qteck/Laboratory-MMC-controller/Images/acquisition_front.jpg

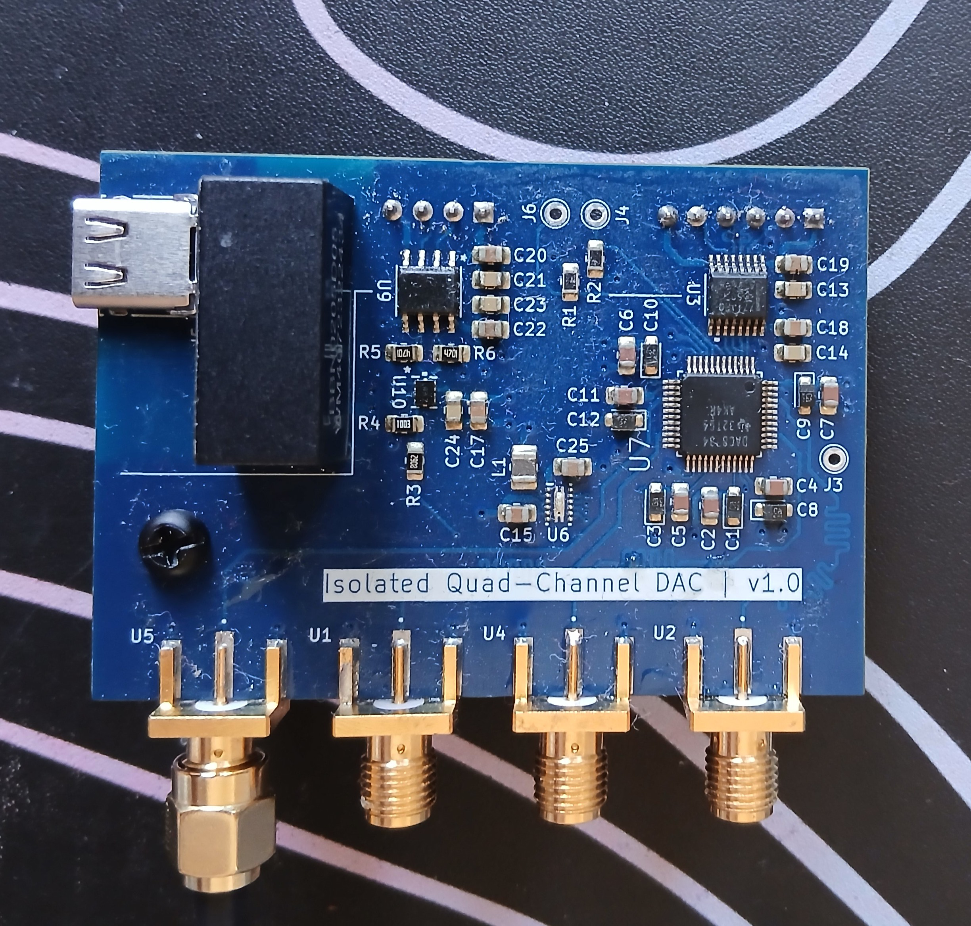
Images/acquisition_front.jpg
