qteck/Laboratory-MMC-controller/Images/df_robot_back.jpg

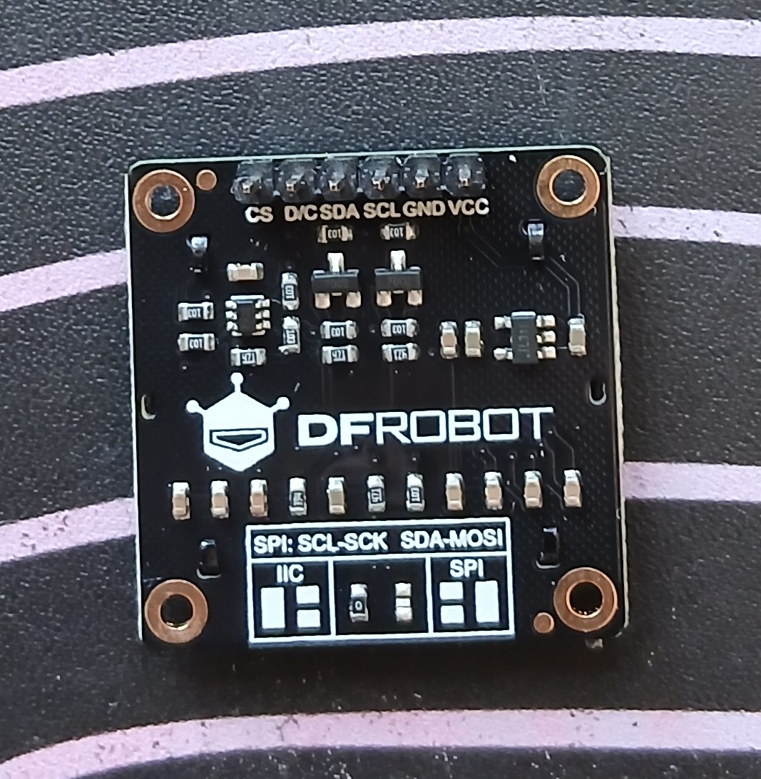
Images/df_robot_back.jpg
