qteck/Laboratory-MMC-controller/Images/df_robot_front.jpg

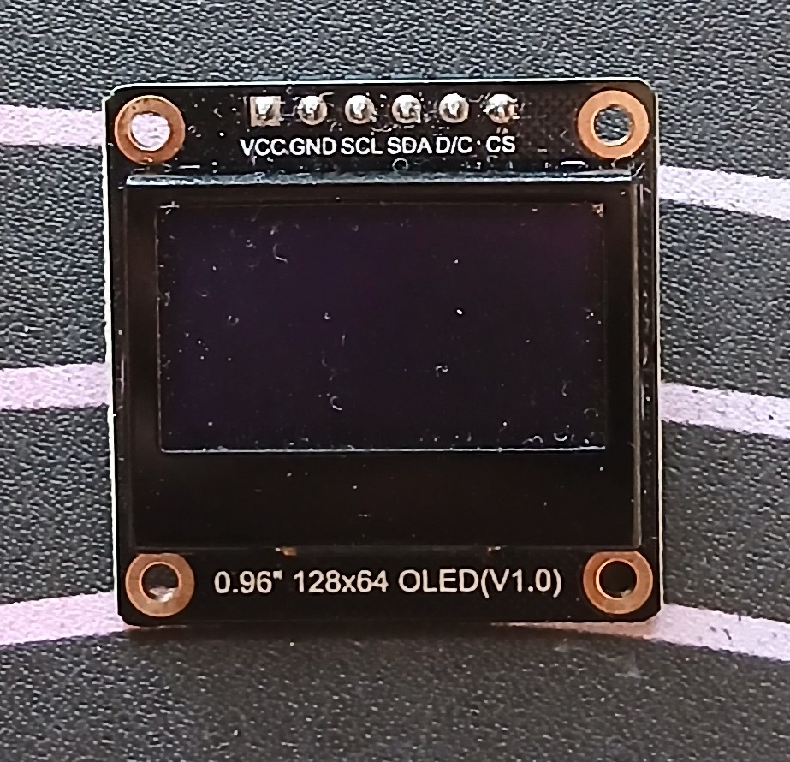
Images/df_robot_front.jpg
