qteck/Laboratory-MMC-controller/Images/pec12r_back.jpg

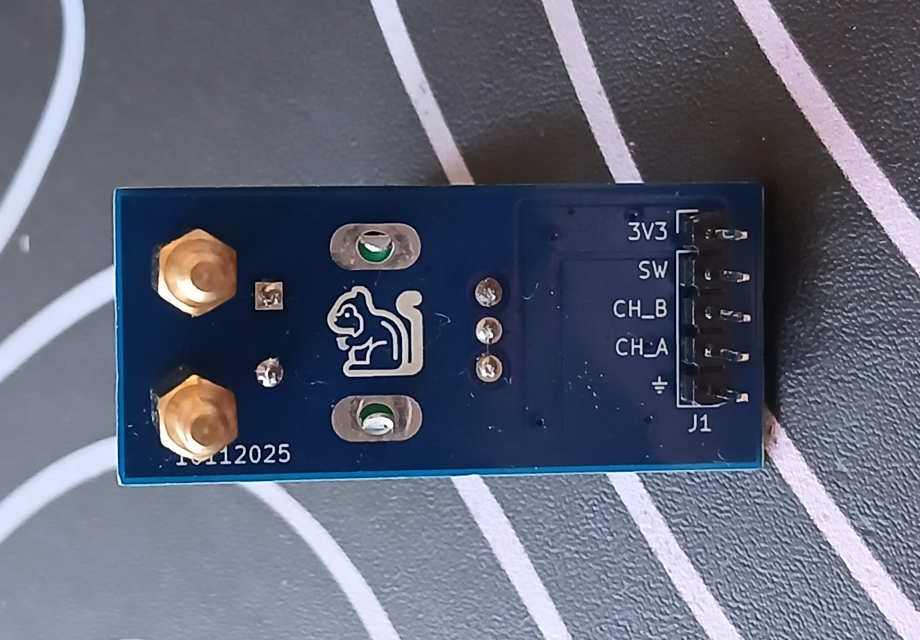
Images/pec12r_back.jpg
