qteck/Laboratory-MMC-controller/Images/pec12r_front.jpg

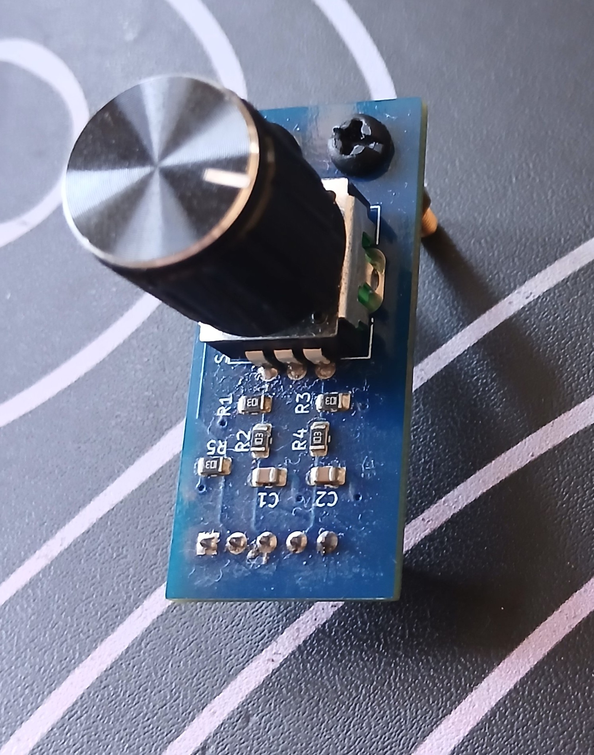
Images/pec12r_front.jpg
