qteck/Laboratory-MMC-controller/KiCad9/PEC12R/PEC12R.png

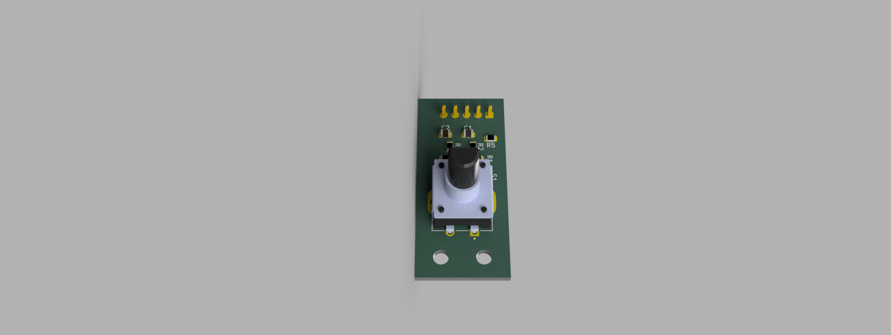
KiCad9/PEC12R/PEC12R.png
