qteck/Laboratory-MMC-controller/KiCad9/uMMC/Images/uMMC4.png

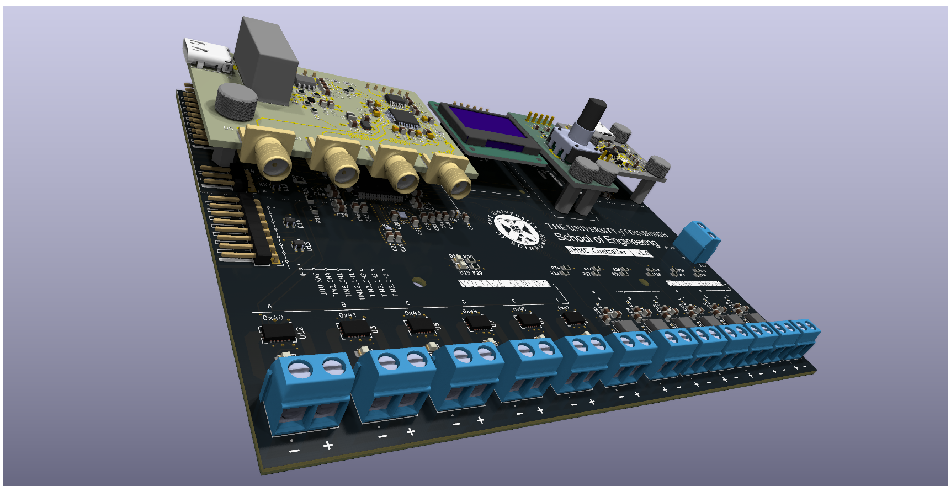
KiCad9/uMMC/Images/uMMC4.png
