qteck/Laboratory-MMC-controller/LTSPICE/F-BRIDGE-4-SM_lower_arm/H-Bridge-4-SM.asc

M1: nmos4; N
M2: pmos4; P
M3: nmos4; N
M4: pmos4; P
M21: nmos4; N
M22: pmos4; P
M23: nmos4; N
M24: pmos4; P
M25: nmos4; N
M26: pmos4; P
M27: nmos4; N
M28: pmos4; P
M29: nmos4; N
M30: pmos4; P
M31: nmos4; N
M32: pmos4; P
M33: nmos4; N
M34: pmos4; P
M35: nmos4; N
M36: pmos4; P
V1: voltage; PULSE({PWM_VINIT} {PWM_VON} 0 1n 1n {T_on} {T_period})
V2: voltage; PULSE({PWM_VINIT} {PWM_VON} {T_delay} 1n 1n {T_on} {T_period})
V3: voltage; 10
V4: voltage; PULSE({PWM_VINIT} {PWM_VON} 0 1m 1m {T_on} {T_period})
V5: voltage; PULSE({PWM_VINIT} {PWM_VON} {T_delay} 1m 1m {T_on} {T_period})
V6: voltage; PULSE({PWM_VINIT} {PWM_VON} {T_on/4} 1m 1m {T_on/2} {T_period})
V7: voltage; PULSE({PWM_VINIT} {PWM_VON} {T_delay+(T_on/4)} 1m 1m {T_on/2} {T_period})
V8: voltage; PULSE({PWM_VINIT} {PWM_VON} {3*T_on/8} 1m 1m {T_on/4} {T_period})
V9: voltage; PULSE({PWM_VINIT} {PWM_VON} {T_delay+(3*T_on/8)} 1m 1m {T_on/4} {T_period})
V10: voltage; 10
V14: voltage; PULSE({PWM_VINIT} {PWM_VON} {7*T_on/16} 1m 1m {T_on/8} {T_period})
V15: voltage; PULSE({PWM_VINIT} {PWM_VON} {T_delay+(7*T_on/16)} 1m 1m {T_on/8} {T_period})
V17: voltage; 10
V18: voltage; 10
V19: voltage; 10
V20: voltage; 10
Named nets: PWM1, PWM2, 0, GND_SM, +VDC, P1_1, P1_2, P2_1, P2_2, P3_1, P3_2, P4_1, P4_2
.MODEL N NMOS LEVEL=1 VTO=2 GAMMA=0.45 PHI=0.9
+NSUB=9e14 LD=0.08e-6 UO=350 LAMBDA=0.1
+TOX=9e-9 PB=0.9 CJ=0.56e-3 CJSW=0.35e-11
+MJ=0.45 MJSW=0.2 CGDO=0.4e-9 JS=1.0e-8
.MODEL P PMOS LEVEL=1 VTO=-3 GAMMA=0.45 PHI=0.9
+NSUB=9e14 LD=0.08e-6 UO=150 LAMBDA=0.1
+TOX=9e-9 PB=0.9 CJ=0.56e-3 CJSW=0.35e-11
+MJ=0.45 MJSW=0.2 CGDO=0.4e-9 JS=1.0e-8
Configuration uses PMOS UP, NMOS DOWN.
The reason for it is simplicity. The set up avoids the need for boostraping the center point.
PMOS ON: 
VSG > |VTH| 
VS - VG > |VTH| 
-VG > -VS + |VTH| 
VG < VS - |VTH| 
 
VG < VDC - |VTH| 
VG < (-10) - |(-3)|
VG < -13V
NMOS ON:
VGS > VTH
VG - VS > VTH 
VG > VS + VTH
 
VG > GND + VTH 
VG > 0 + (+2) 
VG > 2
For complimentary function: 
Just beyond the cut off region: 
PWM>7 
PWM<2
 
Ideally safe Sat Region: 
PWM LOW = 0
PWM HIGH = 10V
.tran 0 1 0
.param D = 0.5 ;50% - max duty cycle
.param PWM_VINIT=20
.param PWM_VON=-20
.param f=10
.param DT=2m
.param DT_offset = (DT/2)
 
.param T_period = 1/f
.param T_delay=0.5*T_period
.param T_on = (T_period*D)-DT_offset
 
.param C=1p
Potential issue: the body diodes. Mostly pointing both up and using NMOS
