qteck/Laboratory-MMC-controller/LTSPICE/F-BRIDGE-4-SM_upper_arm/H-Bridge-4-SM.asc

M1: nmos4; N
M2: pmos4; P
M3: nmos4; N
M4: pmos4; P
M5: nmos4; N
M6: pmos4; P
M7: nmos4; N
M8: pmos4; P
M9: nmos4; N
M10: pmos4; P
M11: nmos4; N
M12: pmos4; P
M13: nmos4; N
M14: pmos4; P
M15: nmos4; N
M16: pmos4; P
M17: nmos4; N
M18: pmos4; P
M19: nmos4; N
M20: pmos4; P
M21: nmos4; N
M22: pmos4; P
M23: nmos4; N
M24: pmos4; P
M25: nmos; BSP89
M26: pmos4; P
M27: pmos4; P
M29: nmos; BSP89
V1: voltage; PULSE(0 {PWM_VON} 0 1m 1m {T_on} {T_period})
V2: voltage; PULSE(0 {PWM_VON} {T_delay} 1m 1m {T_on} {T_period})
V3: voltage; 10v
V4: voltage; PULSE(0 {PWM_VON} 0 1m 1m {T_on} {T_period})
V5: voltage; PULSE(0 {PWM_VON} {T_delay} 1m 1m {T_on} {T_period})
V6: voltage; PULSE(0 {PWM_VON} {T_on/4} 1m 1m {T_on/2} {T_period})
V7: voltage; PULSE(0 {PWM_VON} {T_delay+(T_on/4)} 1m 1m {T_on/2} {T_period})
V8: voltage; PULSE(0 {PWM_VON} {3*T_on/8} 1m 1m {T_on/4} {T_period})
V9: voltage; PULSE(0 {PWM_VON} {T_delay+(3*T_on/8)} 1m 1m {T_on/4} {T_period})
V10: voltage; 10
V11: voltage; 10
V12: voltage; 10
V13: voltage; 10
V14: voltage; PULSE(0 {PWM_VON} {7*T_on/16} 1m 1m {T_on/8} {T_period})
V15: voltage; PULSE(0 {PWM_VON} {T_delay+(7*T_on/16)} 1m 1m {T_on/8} {T_period})
V16: voltage; 10
V17: voltage; 10
V18: voltage; -10
Named nets: PWM1, PWM2, 0, GND_SM, +VDC, P1_1, P1_2, P2_1, P2_2, P3_1, P3_2, P4_1, P4_2
.MODEL N NMOS LEVEL=1 VTO=2 GAMMA=0.45 PHI=0.9
+NSUB=9e14 LD=0.08e-6 UO=350 LAMBDA=0.1
+TOX=9e-9 PB=0.9 CJ=0.56e-3 CJSW=0.35e-11
+MJ=0.45 MJSW=0.2 CGDO=0.4e-9 JS=1.0e-8
.MODEL P PMOS LEVEL=1 VTO=-3 GAMMA=0.45 PHI=0.9
+NSUB=9e14 LD=0.08e-6 UO=150 LAMBDA=0.1
+TOX=9e-9 PB=0.9 CJ=0.56e-3 CJSW=0.35e-11
+MJ=0.45 MJSW=0.2 CGDO=0.4e-9 JS=1.0e-8
Configuration uses PMOS UP, NMOS DOWN.
The reason for it is simplicity. The set up avoids the need for boostraping the center point.
PMOS ON: 
VSG > |VTH| 
VS - VG > |VTH| 
-VG > -VS + |VTH| 
VG < VS - |VTH| 
 
VG < VDC - |VTH| 
VG < 10 - |(-3)|
VG < 7V
NMOS ON:
VGS > VTH
VG - VS > VTH 
VG > VS + VTH
 
VG > GND + VTH 
VG > 0 + (+2) 
VG > 2
For complimentary function: 
Just beyond the cut off region: 
PWM>7 
PWM<2
 
Ideally safe Sat Region: 
PWM LOW = 0
PWM HIGH = 10V
.tran 0 1 0
.param D = 0.5 ;50% - max duty cycle
.param PWM_VON=20
.param f=10
.param DT=2m
.param DT_offset = (DT/2)
 
.param T_period = 1/f
.param T_delay=0.5*T_period
.param T_on = (T_period*D)-DT_offset
 
.param C=1p
Potential issue: the body diodes. Mostly pointing both up and using NMOS
