qteck/Laboratory-MMC-controller/LTSPICE/lower_upper_arm_2sb/2sb.asc

L1: ind; 100m
L2: ind; 100m
L3: ind; 100m
M1: nmos4; N
M2: pmos4; P
M3: nmos4; N
M4: pmos4; P
M5: nmos4; N
M6: pmos4; P
M7: nmos4; N
M8: pmos4; P
R1: res; 50
V1: voltage; PULSE({PWM_VINIT_L} {PWM_VON_L} 0 1n 1n {T_on} {T_period})
V2: voltage; PULSE({PWM_VINIT_L} {PWM_VON_L} {T_delay} 1n 1n {T_on} {T_period})
V4: voltage; 10
V5: voltage; PULSE({PWM_VINIT_H} {PWM_VON_H} 0 1m 1m {T_on} {T_period})
V6: voltage; PULSE({PWM_VINIT_H} {PWM_VON_H} {T_delay} 1m 1m {T_on} {T_period})
V8: voltage; 10
Named nets: PWM1_L, PWM2_L, 0, GND_SM, PWM1_H, PWM2_H
.MODEL N NMOS LEVEL=1 VTO=2 GAMMA=0.45 PHI=0.9
+NSUB=9e14 LD=0.08e-6 UO=350 LAMBDA=0.1
+TOX=9e-9 PB=0.9 CJ=0.56e-3 CJSW=0.35e-11
+MJ=0.45 MJSW=0.2 CGDO=0.4e-9 JS=1.0e-8
.MODEL P PMOS LEVEL=1 VTO=-3 GAMMA=0.45 PHI=0.9
+NSUB=9e14 LD=0.08e-6 UO=150 LAMBDA=0.1
+TOX=9e-9 PB=0.9 CJ=0.56e-3 CJSW=0.35e-11
+MJ=0.45 MJSW=0.2 CGDO=0.4e-9 JS=1.0e-8
.param PWM_VINIT_H=0
.param PWM_VON_H=20
 
.param PWM_VINIT_L=20
.param PWM_VON_L=-20
 

.param D = 0.5 ;50% - max duty cycle
 

.param f=10
.param DT=2m
.param DT_offset = (DT/2)
 
.param T_period = 1/f
.param T_delay=0.5*T_period
.param T_on = (T_period*D)-DT_offset
.tran 1
This version produce 0 and +10V 
and 0 and -10V 
 
But the center point gets grounded and the subtraction wont happen. 
The GND are attached to the modules, because they have better defined square wave response when the GND is there.
