qteck/Laboratory-MMC-controller/LTSPICE/Scalling/Draft1.asc

R1: res; 40k
R2: res; 10k
R3: res; 100k
R4: res; 100k
R5: res; 6Meg
V1: voltage; 1.8
V2: voltage; 7.2
Named nets: 0
.tran 10m
