qteck/Laboratory-MMC-controller/LTSPICE/uMMC/uMMC.asc

C1: cap; {C}
C2: cap; {C}
C3: cap; {C}
C4: cap; {C}
V1: voltage; 10
V2: voltage; 10
V3: voltage; PULSE(0 {PWM_VON} 0 1m 1m {T_on} {T_period})
V4: voltage; PULSE(0 {PWM_VON} {T_delay} 1m 1m {T_on} {T_period})
X1: H-Bridge-only
X2: H-Bridge-only
X3: H-Bridge-only
X4: H-Bridge-only
Named nets: -DC, +DC, 0, PWM1, PWM2, AC
.param C=1m
.tran 0.1
.param D = 0.5 ;50% - max duty cycle
.param PWM_VON=20
.param f=50
.param DT=2m
.param DT_offset = (DT/2)
 
.param T_period = 1/f
.param T_delay=0.5*T_period
.param T_on = (T_period*D)-DT_offset
