qteck/Laboratory-MMC-controller/KiCad9/DAC8734/LTSPICE/divider_network_vmon.asc

R1: res; 40k
R2: res; 10k
R3: res; 100k
R4: res; 100k
R5: res; 6Meg
R6: res; 40k
R7: res; 10k
R8: res; 100k
R9: res; 100k
R10: res; 6Meg
V1: voltage; 1.8
V2: voltage; 7.2
V3: voltage; 1.8
V4: voltage; SINE(0 3.6 100k)
Named nets: 0
.tran 10m
