qteck/Laboratory-MMC-controller/KiCad9/DAC8734/LTSPICE/Draft1.asc

D1: diode
D2: diode
M1: nmos; Si7336ADP
M2: nmos; BSC150N03LD
R1: res; 4.7k
R2: res; 10k
R3: res; 1k
R4: res; 1k
V1: voltage; 3.3
V2: voltage; 3.3
V3: voltage; 3.3
V4: voltage; 10
Named nets: 0
.tran 1m
