qteck/Laboratory-MMC-controller/KiCad9/DAC8734/LTSPICE/driving_led.asc

D1: diode
D2: diode
D3: diode
M1: nmos; Si7336ADP
M2: nmos; BSC150N03LD
M3: nmos; Si7336ADP
M4: pmos
R1: res; 4.7k
R2: res; 10k
R3: res; 1k
R4: res; 1k
R5: res; 1k
R6: res; 1k
V1: voltage; 5
V2: voltage; 5
V3: voltage; 5
V4: voltage; 5
V5: voltage; 5
V6: voltage; 5
Named nets: 0
.tran 1m
open drain
M1 on -> D2 off
M1 off -> D2 on
alert
alert
alert is, float or gnd
when float - supply balanced
no current flows
the alert pin will be low for most of the time, meaning the drain will float. 
this means that current will flow, when not necesary, and the diode will be on when m1 is off. 
the alert pin can be reversed but, this means that when there is no fault, m1 is on, 
pulling current down from r4, consuming unnecesary current
alert
M3 ON -> M4 ON
M3 OFF -> M4 OFF
